BobbyTheII/kit_de_geometrie/Photo/20250502_154723.jpg

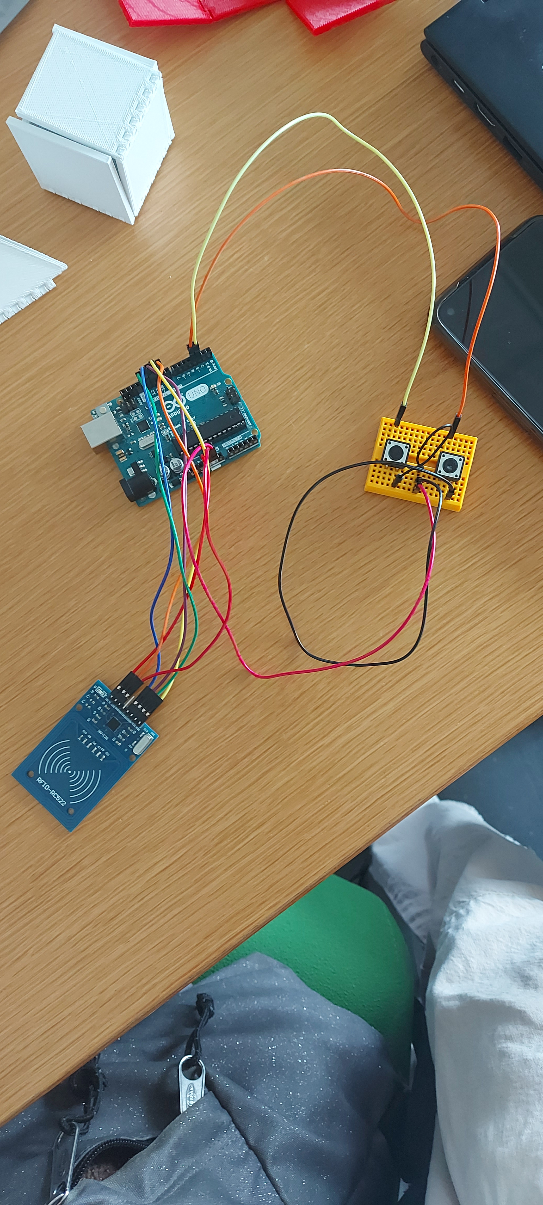
Photo/20250502_154723.jpg
