BobbyTheII/kit_de_geometrie/Photo/20250521_115105.jpg

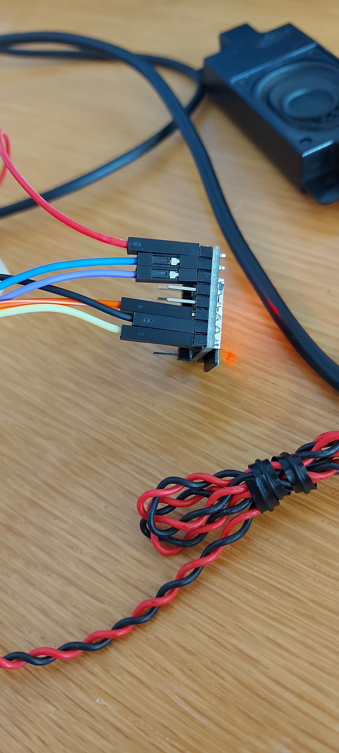
Photo/20250521_115105.jpg
