BobbyTheII/kit_de_geometrie/Photo/20250526_151836.jpg

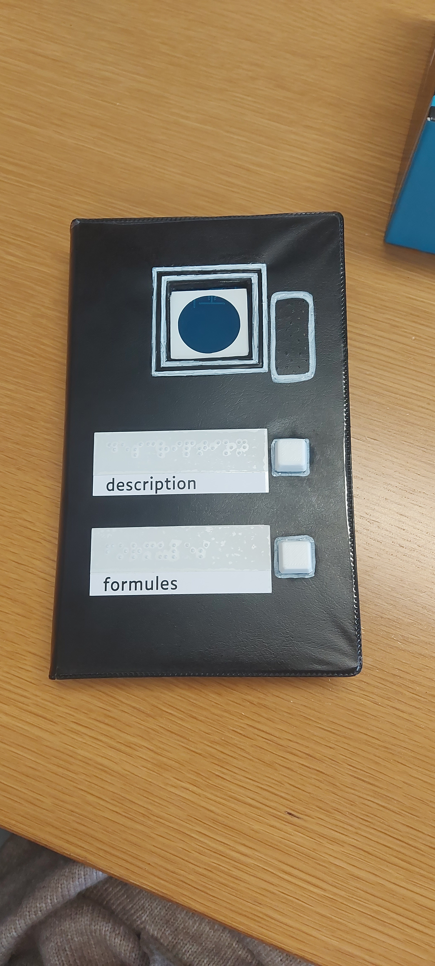
Photo/20250526_151836.jpg
